mehrantsi/MSAP-2/Schematics/PNGs/ADDRESS_PATH.png

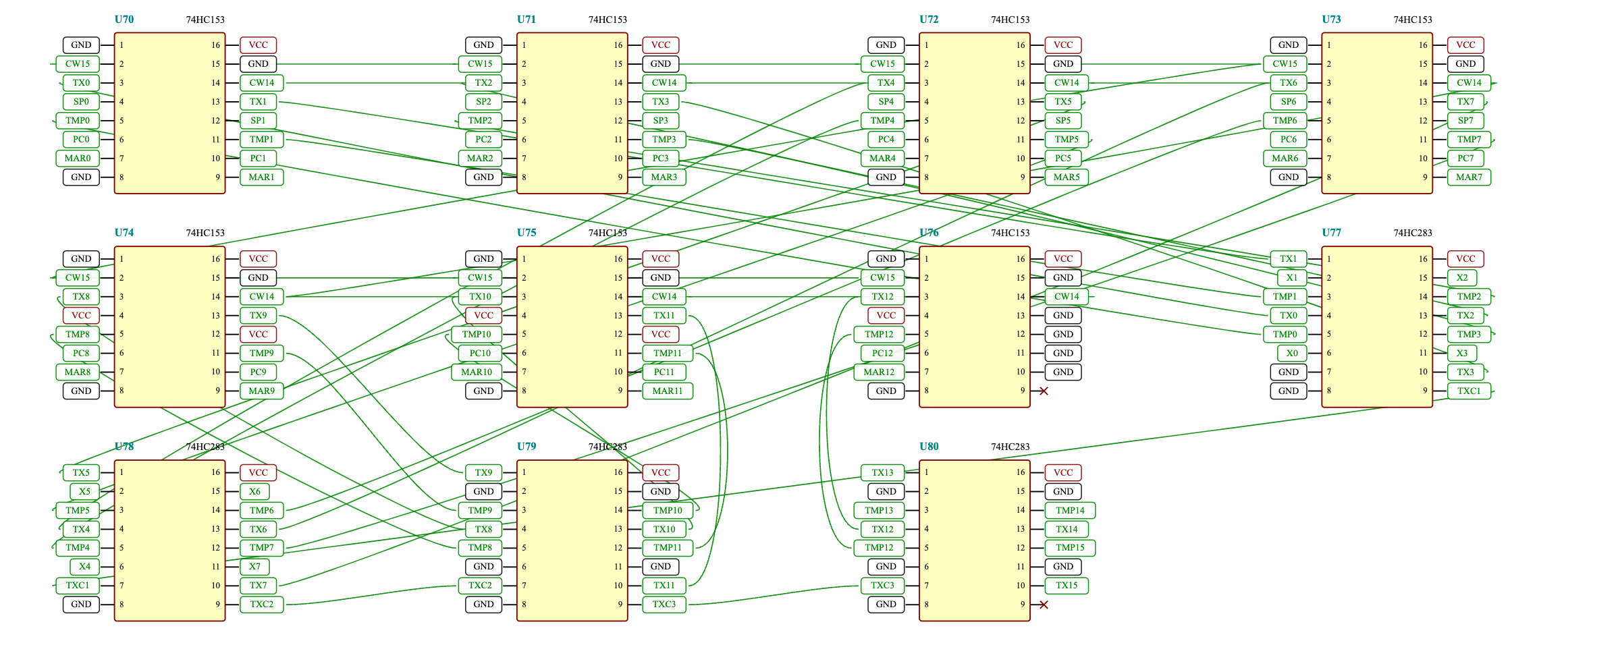
Schematics/PNGs/ADDRESS_PATH.png
