mehrantsi/MSAP-2/Schematics/PNGs/ALU_74HC181.png

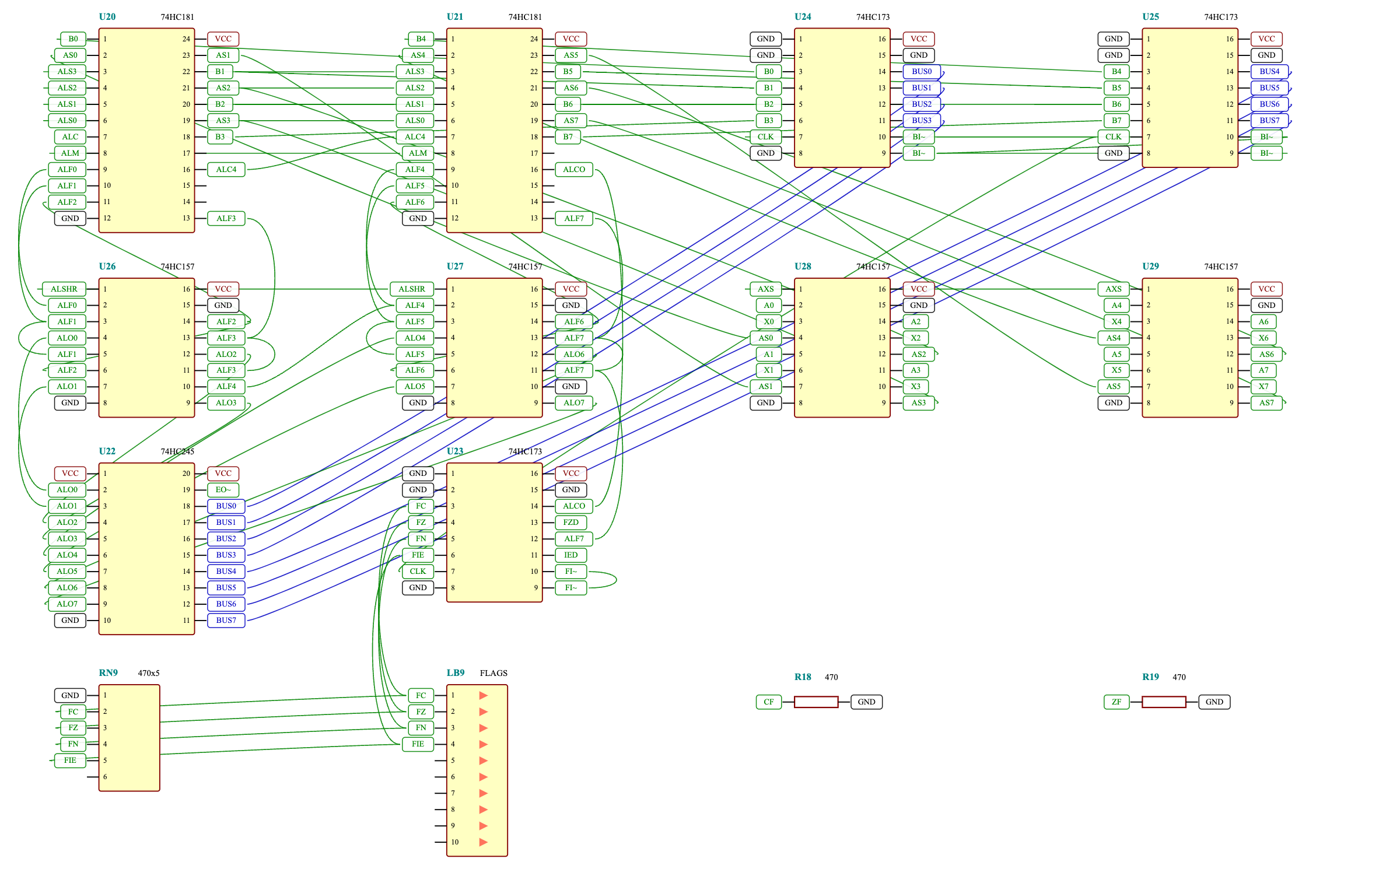
Schematics/PNGs/ALU_74HC181.png
