mehrantsi/MSAP-2/Schematics/PNGs/CLOCK.png

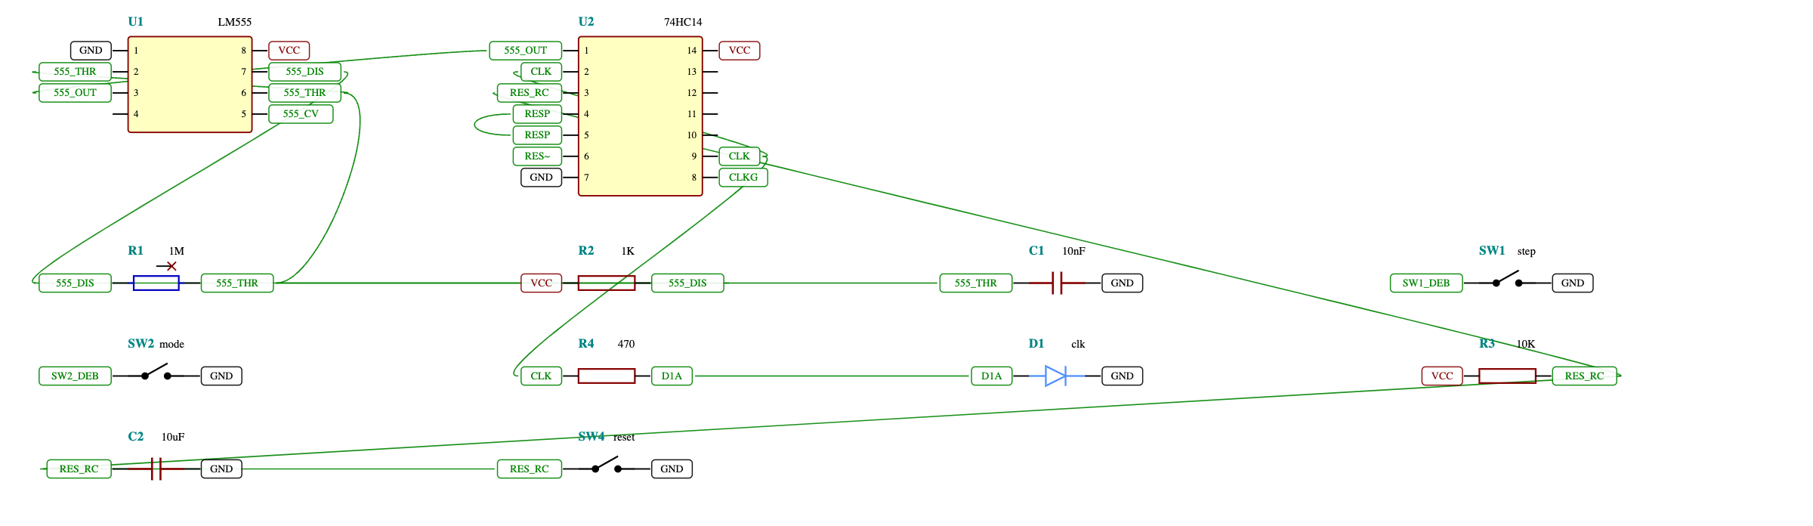
Schematics/PNGs/CLOCK.png
