mehrantsi/MSAP-2/Schematics/PNGs/TERMINAL_DISK_IO.png

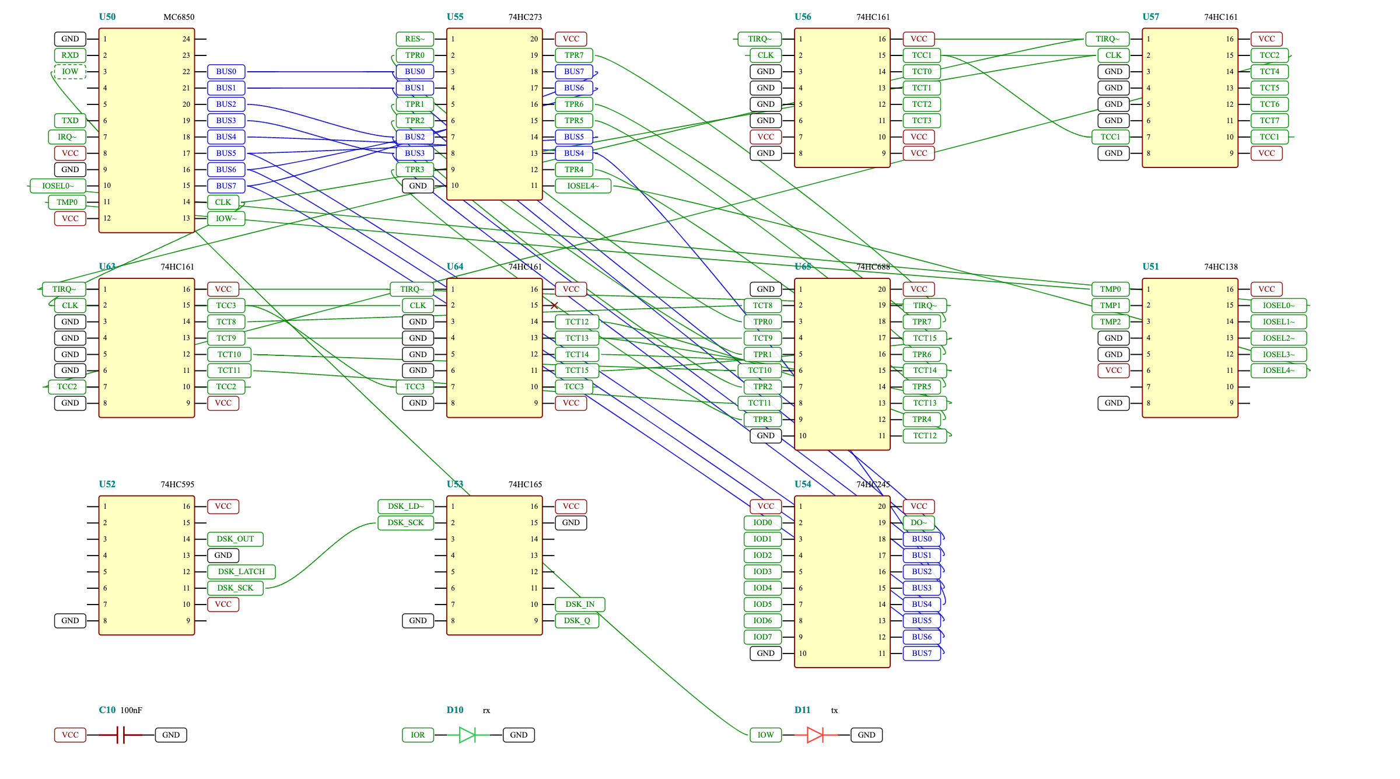
Schematics/PNGs/TERMINAL_DISK_IO.png
